hisea/flake/docs/img/plate.jpg

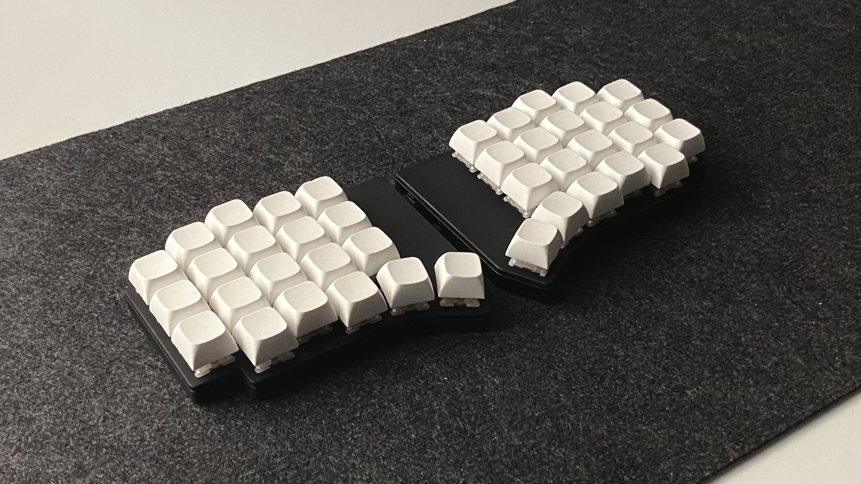
docs/img/plate.jpg
