hisea/flake/docs/img/stacked.jpg

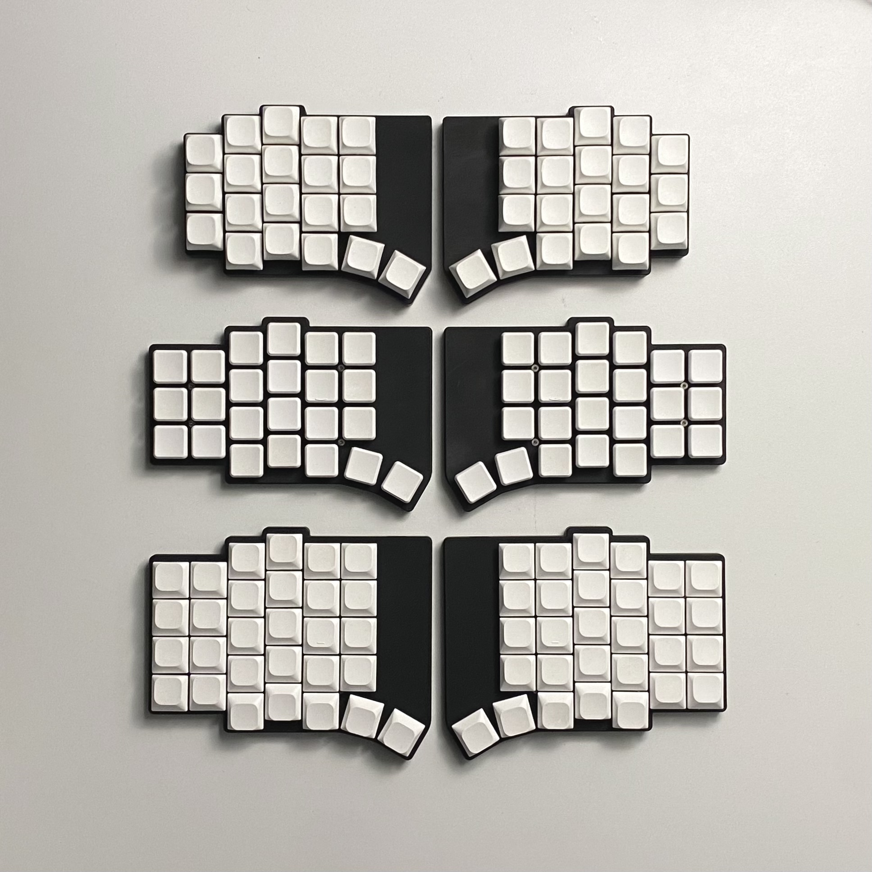
docs/img/stacked.jpg
