hisea/flake/enclosure/L/Enclosure-L.FCStd

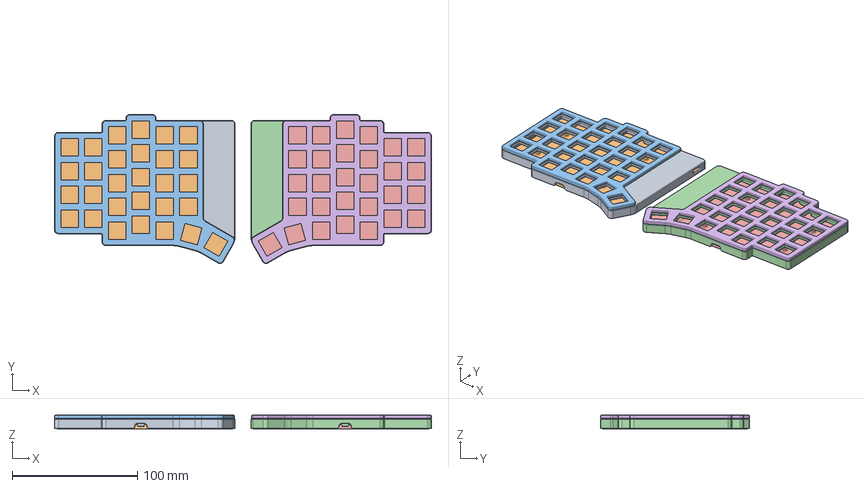
[picture p29: CAD file, 2025-02-06]
enclosure/L/Enclosure-L.FCStd
301.0 x 119.0 x 10.8 mm
Top-Left
Bottom-Left
Plate-Left
Top-Right
Bottom-Right
Plate-Right
