hisea/flake/enclosure/M/Enclosure-M.FCStd

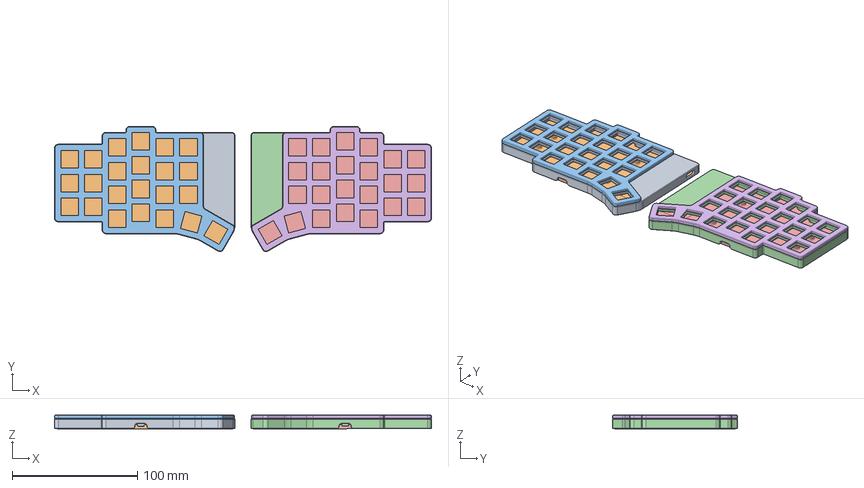
[picture p30: CAD file, 2025-02-06]
enclosure/M/Enclosure-M.FCStd
301.0 x 100.0 x 10.8 mm
Top-Left
Bottom-Left
Plate-Left
Top-Right
Bottom-Right
Plate-Right
