hisea/flake/pcb/L/right.kicad_sch

## KiCad design pcb/L/right.kicad_sch (2025-01-11)

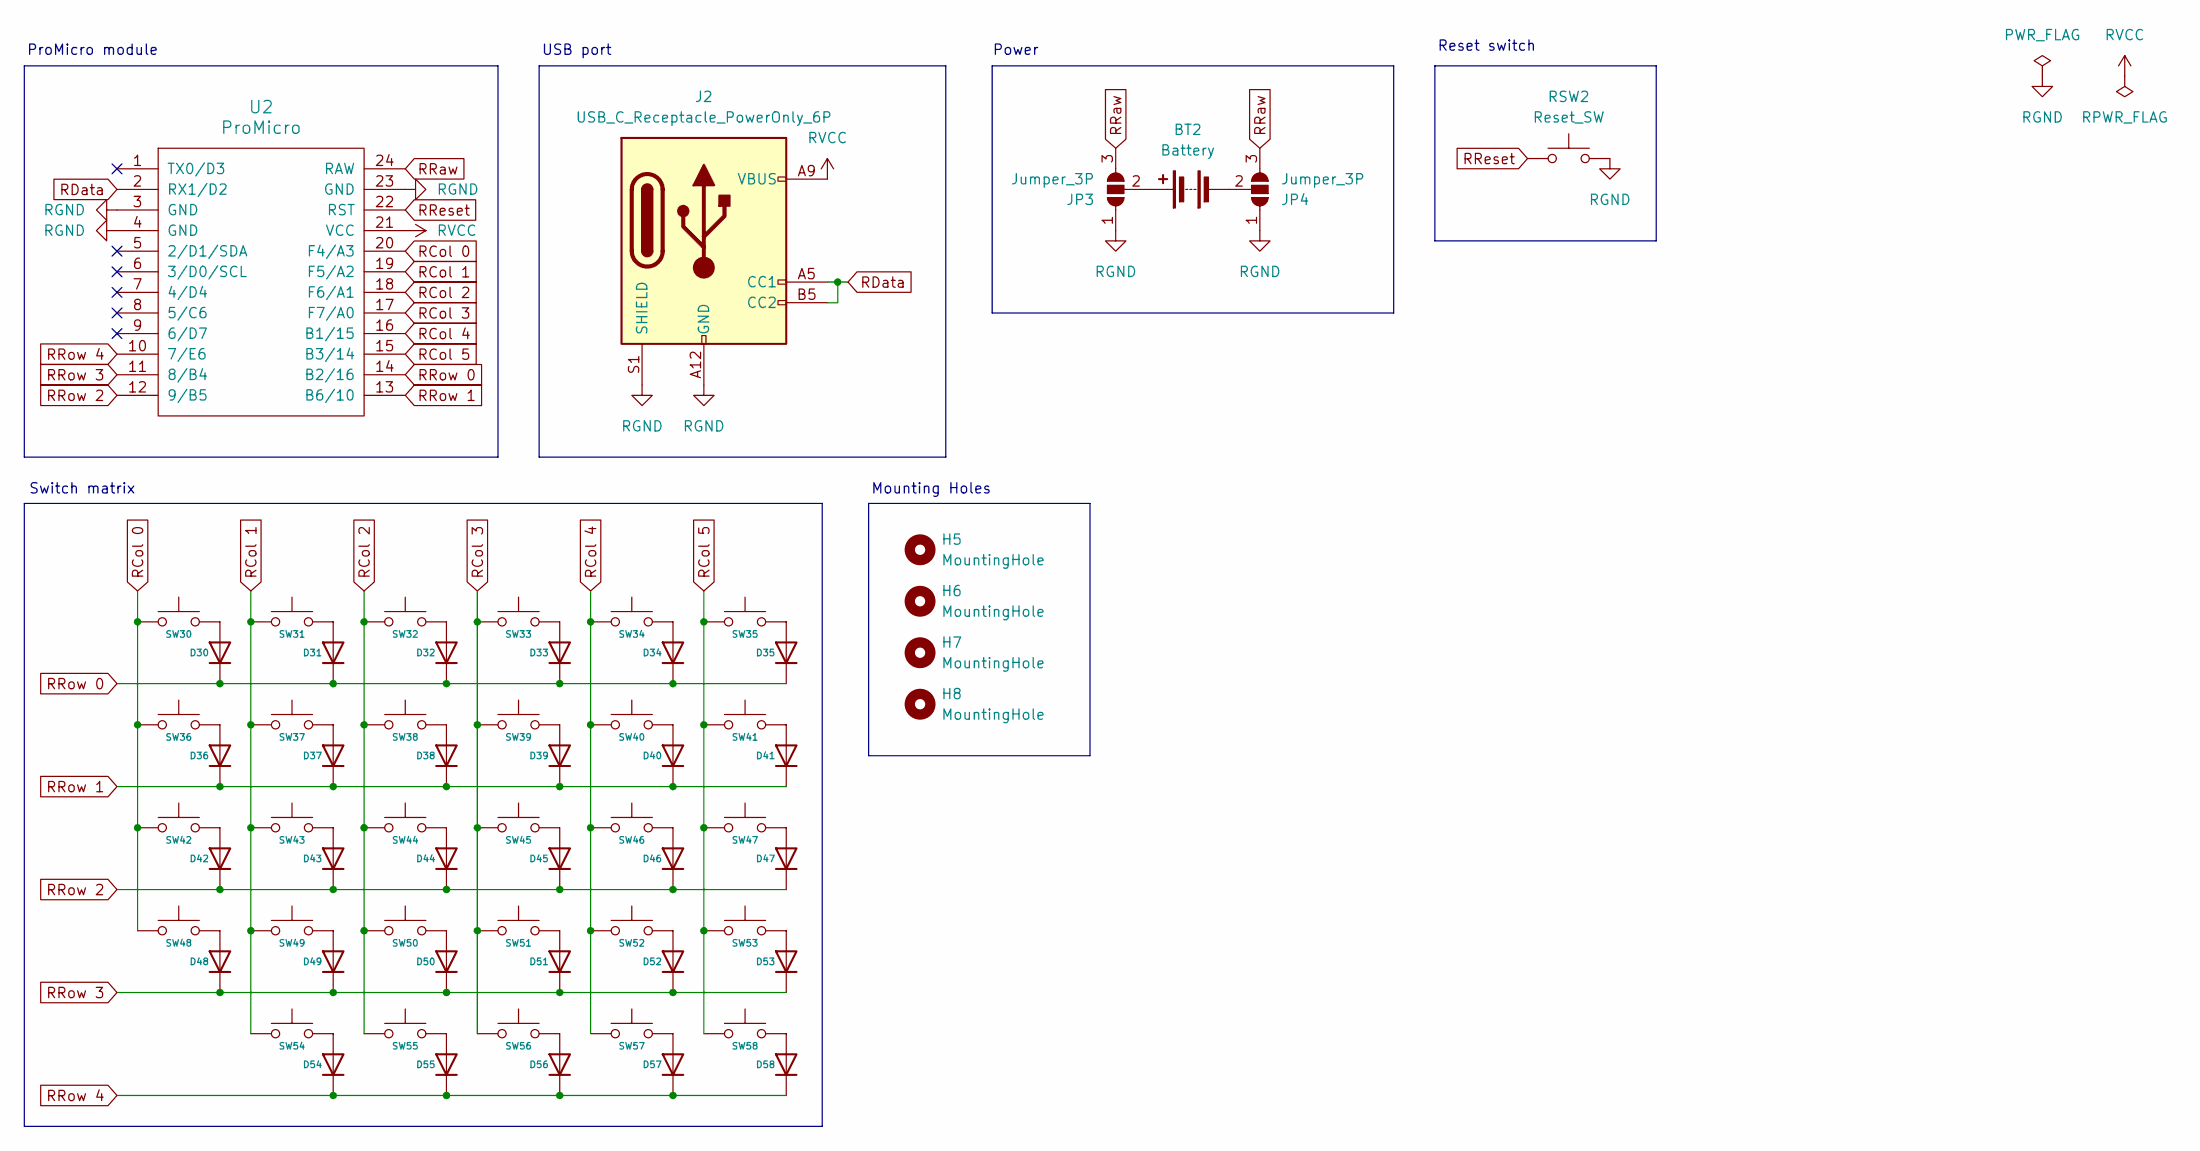
[picture p52: schematic right.kicad_sch]

Parts:
BT2: Battery; JST_1.25mm_mid-mount
D30, D31, D32, D33, D34, D35, D36, D37, D38, D39, D40, D41, D42, D43, D44, D45, D46, D47, D48, D49, D50, D51, D52, D53, D54, D55, D56, D57, D58: D; D_SOD-323_HandSoldering
H5, H6, H7, H8: MountingHole; MountingHole_2.2mm_M2_DIN965
J2: USB_C_Receptacle_PowerOnly_6P; USB-C_6Pin_Mid-mount
JP3, JP4: Jumper_3P; SolderJumper-3_P
RSW2: Reset_SW; TS-1289VE-4
SW30, SW31, SW32, SW33, SW34, SW35, SW36, SW37, SW38, SW39, SW40, SW41, SW42, SW43, SW44, SW45, SW46, SW47, SW48, SW49, SW50, SW51, SW52, SW53, SW54, SW55, SW56, SW57, SW58: SW_Push; SW_MX_Choc-v1v2_Hotswap
U2: ProMicro; ProMicro_SMD

Connections:
unnamed: BT2.1 (+), JP3.2 (C)
unnamed: BT2.2 (-), JP4.2 (C)
unnamed: D30.2 (A), SW30.2
unnamed: D31.2 (A), SW31.2
unnamed: D32.2 (A), SW32.2
unnamed: D33.2 (A), SW33.2
unnamed: D34.2 (A), SW34.2
unnamed: D35.2 (A), SW35.2
unnamed: D36.2 (A), SW36.2
unnamed: D37.2 (A), SW37.2
unnamed: D38.2 (A), SW38.2
unnamed: D39.2 (A), SW39.2
unnamed: D40.2 (A), SW40.2
unnamed: D41.2 (A), SW41.2
unnamed: D42.2 (A), SW42.2
unnamed: D43.2 (A), SW43.2
unnamed: D44.2 (A), SW44.2
unnamed: D45.2 (A), SW45.2
unnamed: D46.2 (A), SW46.2
unnamed: D47.2 (A), SW47.2
unnamed: D48.2 (A), SW48.2
unnamed: D49.2 (A), SW49.2
unnamed: D50.2 (A), SW50.2
unnamed: D51.2 (A), SW51.2
unnamed: D52.2 (A), SW52.2
unnamed: D53.2 (A), SW53.2
unnamed: D54.2 (A), SW54.2
unnamed: D55.2 (A), SW55.2
unnamed: D56.2 (A), SW56.2
unnamed: D57.2 (A), SW57.2
unnamed: D58.2 (A), SW58.2
RCol 0: SW30.1, SW36.1, SW42.1, SW48.1, U2.20 (F4/A3)
RCol 1: SW31.1, SW37.1, SW43.1, SW49.1, SW54.1, U2.19 (F5/A2)
RCol 2: SW32.1, SW38.1, SW44.1, SW50.1, SW55.1, U2.18 (F6/A1)
RCol 3: SW33.1, SW39.1, SW45.1, SW51.1, SW56.1, U2.17 (F7/A0)
RCol 4: SW34.1, SW40.1, SW46.1, SW52.1, SW57.1, U2.16 (B1/15)
RCol 5: SW35.1, SW41.1, SW47.1, SW53.1, SW58.1, U2.15 (B3/14)
RData: J2.A5 (CC1), J2.B5 (CC2), U2.2 (RX1/D2)
RGND: J2.A12 (GND), J2.B12 (GND), J2.S1 (SHIELD), JP3.1 (A), JP4.1 (A), RSW2.2, U2.3 (GND), U2.4 (GND), U2.23 (GND)
RRaw: JP3.3 (B), JP4.3 (B), U2.24 (RAW)
RReset: RSW2.1, U2.22 (RST)
RRow 0: D30.1 (K), D31.1 (K), D32.1 (K), D33.1 (K), D34.1 (K), D35.1 (K), U2.14 (B2/16)
RRow 1: D36.1 (K), D37.1 (K), D38.1 (K), D39.1 (K), D40.1 (K), D41.1 (K), U2.13 (B6/10)
RRow 2: D42.1 (K), D43.1 (K), D44.1 (K), D45.1 (K), D46.1 (K), D47.1 (K), U2.12 (9/B5)
RRow 3: D48.1 (K), D49.1 (K), D50.1 (K), D51.1 (K), D52.1 (K), D53.1 (K), U2.11 (8/B4)
RRow 4: D54.1 (K), D55.1 (K), D56.1 (K), D57.1 (K), D58.1 (K), U2.10 (7/E6)
RVCC: J2.A9 (VBUS), J2.B9 (VBUS), U2.21 (VCC)

Notes on the sheet:
Switch matrix
Mounting Holes
USB port
Power
ProMicro module
Reset switch
