hisea/flake/pcb/M,S/left.kicad_sch

## KiCad design pcb/M,S/left.kicad_sch (2025-06-08)

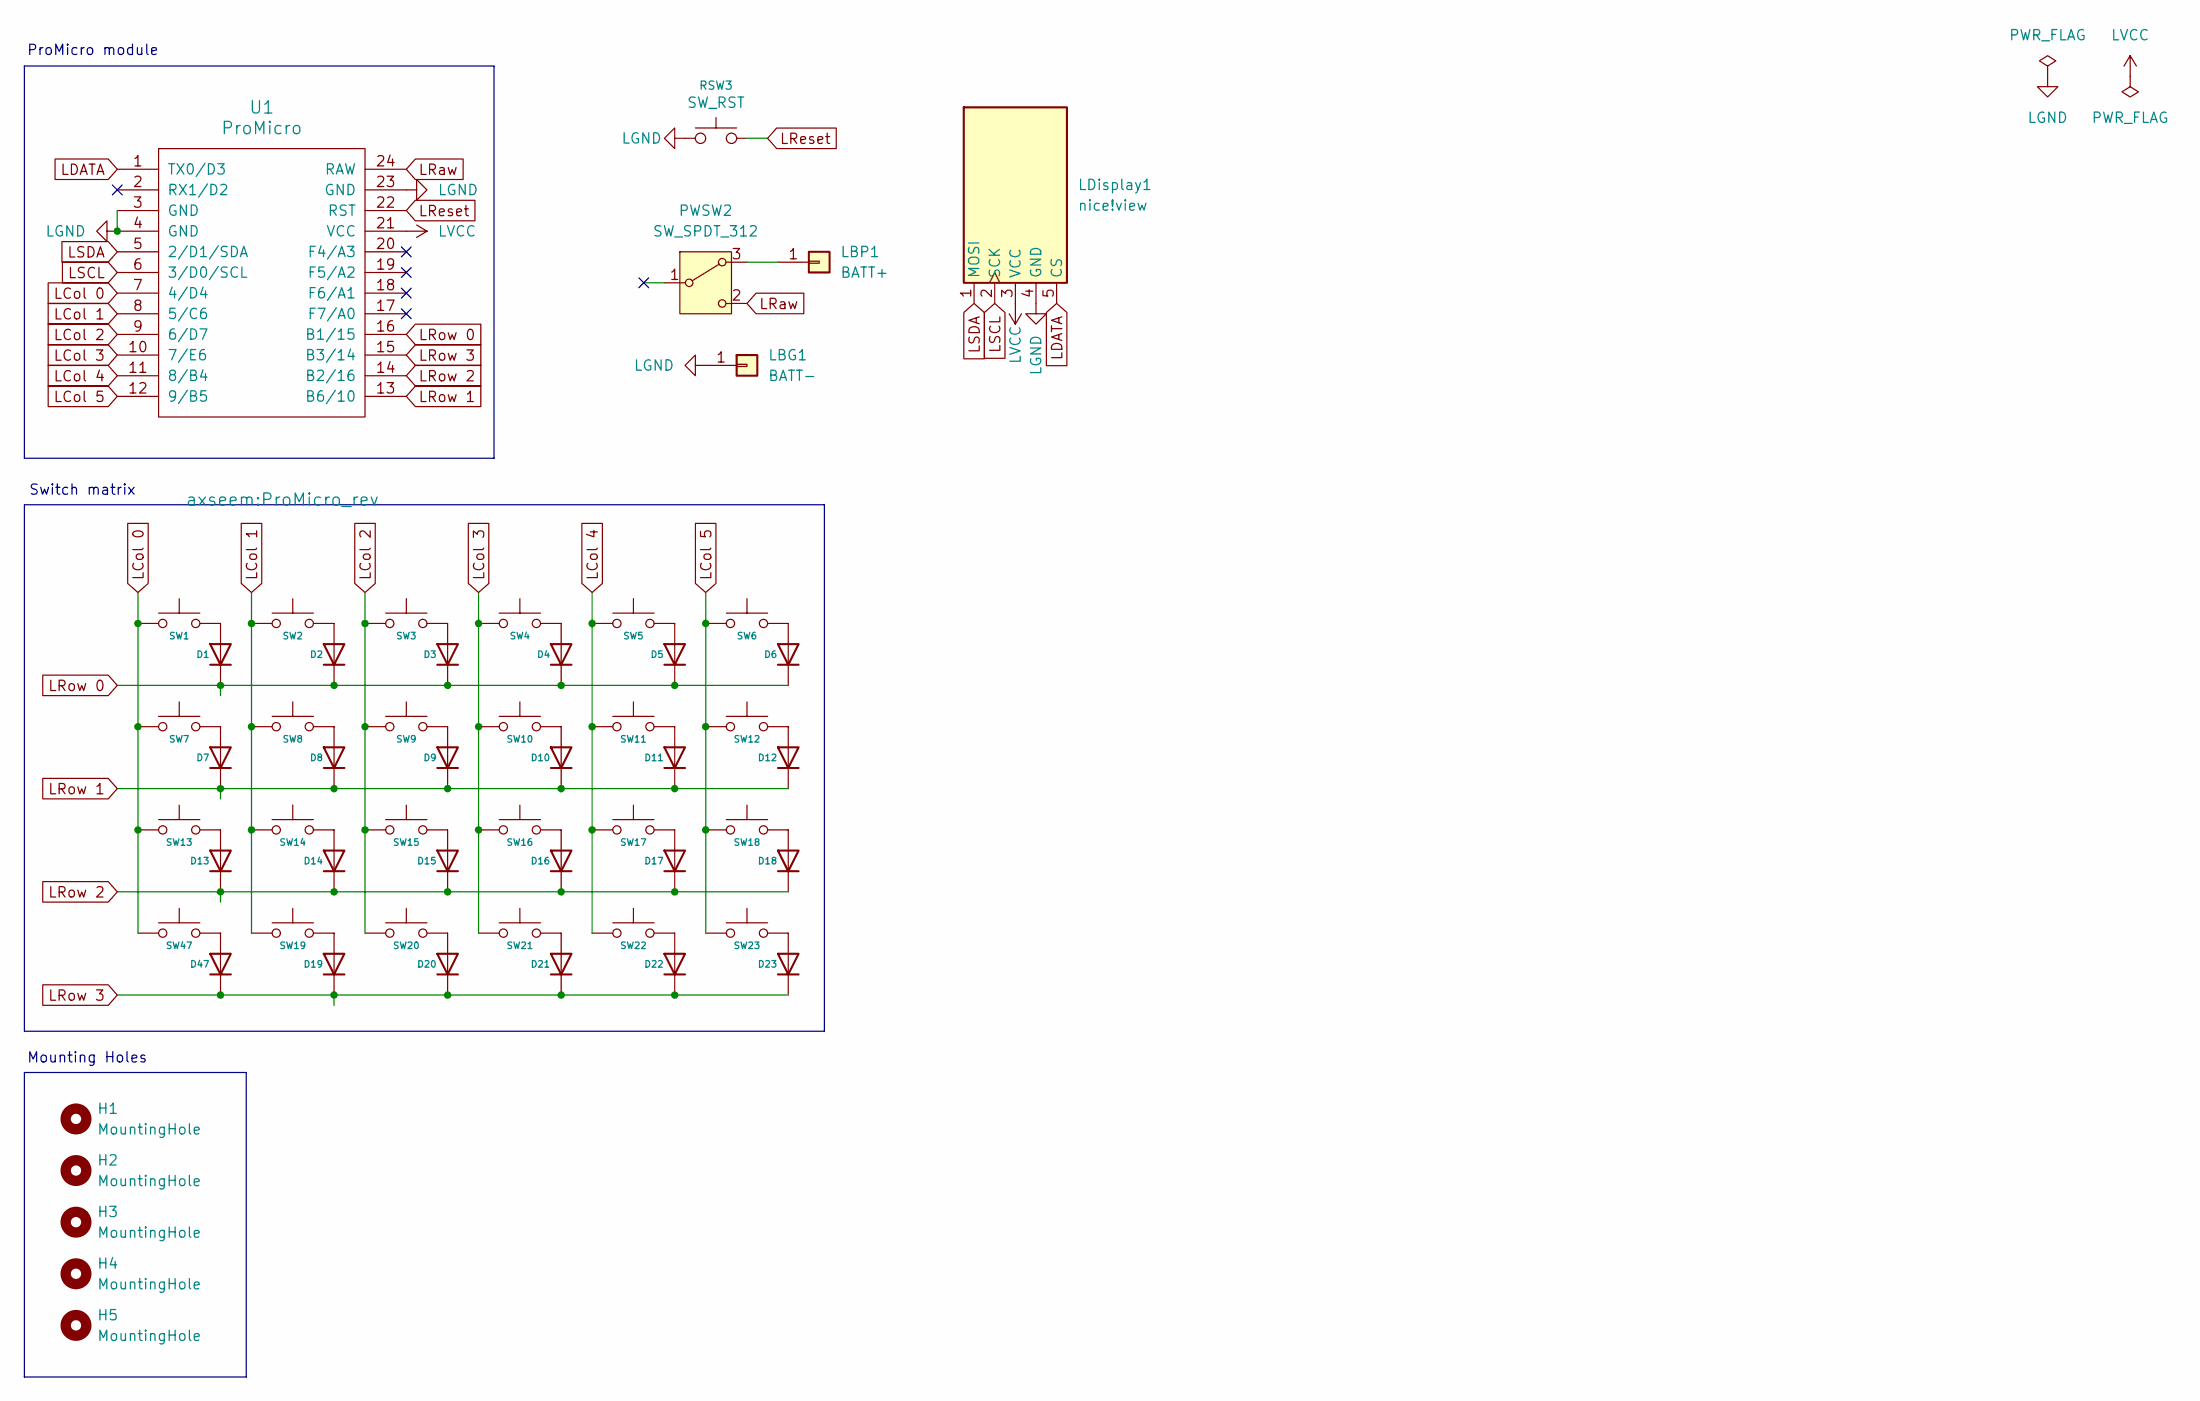
[picture p53: schematic left.kicad_sch]

Parts:
D1, D2, D3, D4, D5, D6, D7, D8, D9, D10, D11, D12, D13, D14, D15, D16, D17, D18, D19, D20, D21, D22, D23, D47: D; D_SOD-323_HandSoldering
H1, H2, H3, H4, H5: MountingHole; MountingHole_2.2mm_M2_DIN965
LBG1: BATT-; 1pin_conn
LBP1: BATT+; 1pin_conn
LDisplay1: nice!view; nice_view_1side
PWSW2: SW_SPDT_312; switch-MSK-12C02-smd
RSW3: SW_RST; TACT_SWITCH_TVBP06
SW1, SW2, SW3, SW4, SW5, SW6, SW7, SW8, SW9, SW10, SW11, SW12, SW13, SW14, SW15, SW16, SW17, SW18, SW19, SW20, SW21, SW22, SW23, SW47: SW_Push; SW_MX_Choc-v1v2_Hotswap
U1: ProMicro; ProMicro_rev

Connections:
LCol 0: SW1.1, SW7.1, SW13.1, SW47.1, U1.7 (4/D4)
LCol 1: SW2.1, SW8.1, SW14.1, SW19.1, U1.8 (5/C6)
LCol 2: SW3.1, SW9.1, SW15.1, SW20.1, U1.9 (6/D7)
LCol 3: SW4.1, SW10.1, SW16.1, SW21.1, U1.10 (7/E6)
LCol 4: SW5.1, SW11.1, SW17.1, SW22.1, U1.11 (8/B4)
LCol 5: SW6.1, SW12.1, SW18.1, SW23.1, U1.12 (9/B5)
LDATA: LDisplay1.5 (CS), U1.1 (TX0/D3)
LGND: LBG1.1, LDisplay1.4 (GND), RSW3.1, U1.3 (GND), U1.4 (GND), U1.23 (GND)
LRaw: PWSW2.2 (C), U1.24 (RAW)
LReset: RSW3.2, U1.22 (RST)
LRow 0: D1.1 (K), D2.1 (K), D3.1 (K), D4.1 (K), D5.1 (K), D6.1 (K), U1.16 (B1/15)
LRow 1: D7.1 (K), D8.1 (K), D9.1 (K), D10.1 (K), D11.1 (K), D12.1 (K), U1.13 (B6/10)
LRow 2: D13.1 (K), D14.1 (K), D15.1 (K), D16.1 (K), D17.1 (K), D18.1 (K), U1.14 (B2/16)
LRow 3: D19.1 (K), D20.1 (K), D21.1 (K), D22.1 (K), D23.1 (K), D47.1 (K), U1.15 (B3/14)
LSCL: LDisplay1.2 (SCK), U1.6 (3/D0/SCL)
LSDA: LDisplay1.1 (MOSI), U1.5 (2/D1/SDA)
LVCC: LDisplay1.3 (VCC), U1.21 (VCC)
unnamed: D1.2 (A), SW1.2
unnamed: D2.2 (A), SW2.2
unnamed: D3.2 (A), SW3.2
unnamed: D4.2 (A), SW4.2
unnamed: D5.2 (A), SW5.2
unnamed: D6.2 (A), SW6.2
unnamed: D7.2 (A), SW7.2
unnamed: D8.2 (A), SW8.2
unnamed: D9.2 (A), SW9.2
unnamed: D10.2 (A), SW10.2
unnamed: D11.2 (A), SW11.2
unnamed: D12.2 (A), SW12.2
unnamed: D13.2 (A), SW13.2
unnamed: D14.2 (A), SW14.2
unnamed: D15.2 (A), SW15.2
unnamed: D16.2 (A), SW16.2
unnamed: D17.2 (A), SW17.2
unnamed: D18.2 (A), SW18.2
unnamed: D19.2 (A), SW19.2
unnamed: D20.2 (A), SW20.2
unnamed: D21.2 (A), SW21.2
unnamed: D22.2 (A), SW22.2
unnamed: D23.2 (A), SW23.2
unnamed: D47.2 (A), SW47.2
unnamed: LBP1.1, PWSW2.3 (A)

Notes on the sheet:
Switch matrix
Mounting Holes
ProMicro module
