hisea/flake/pcb/M,S/right.kicad_sch

## KiCad design pcb/M,S/right.kicad_sch (2025-06-08)

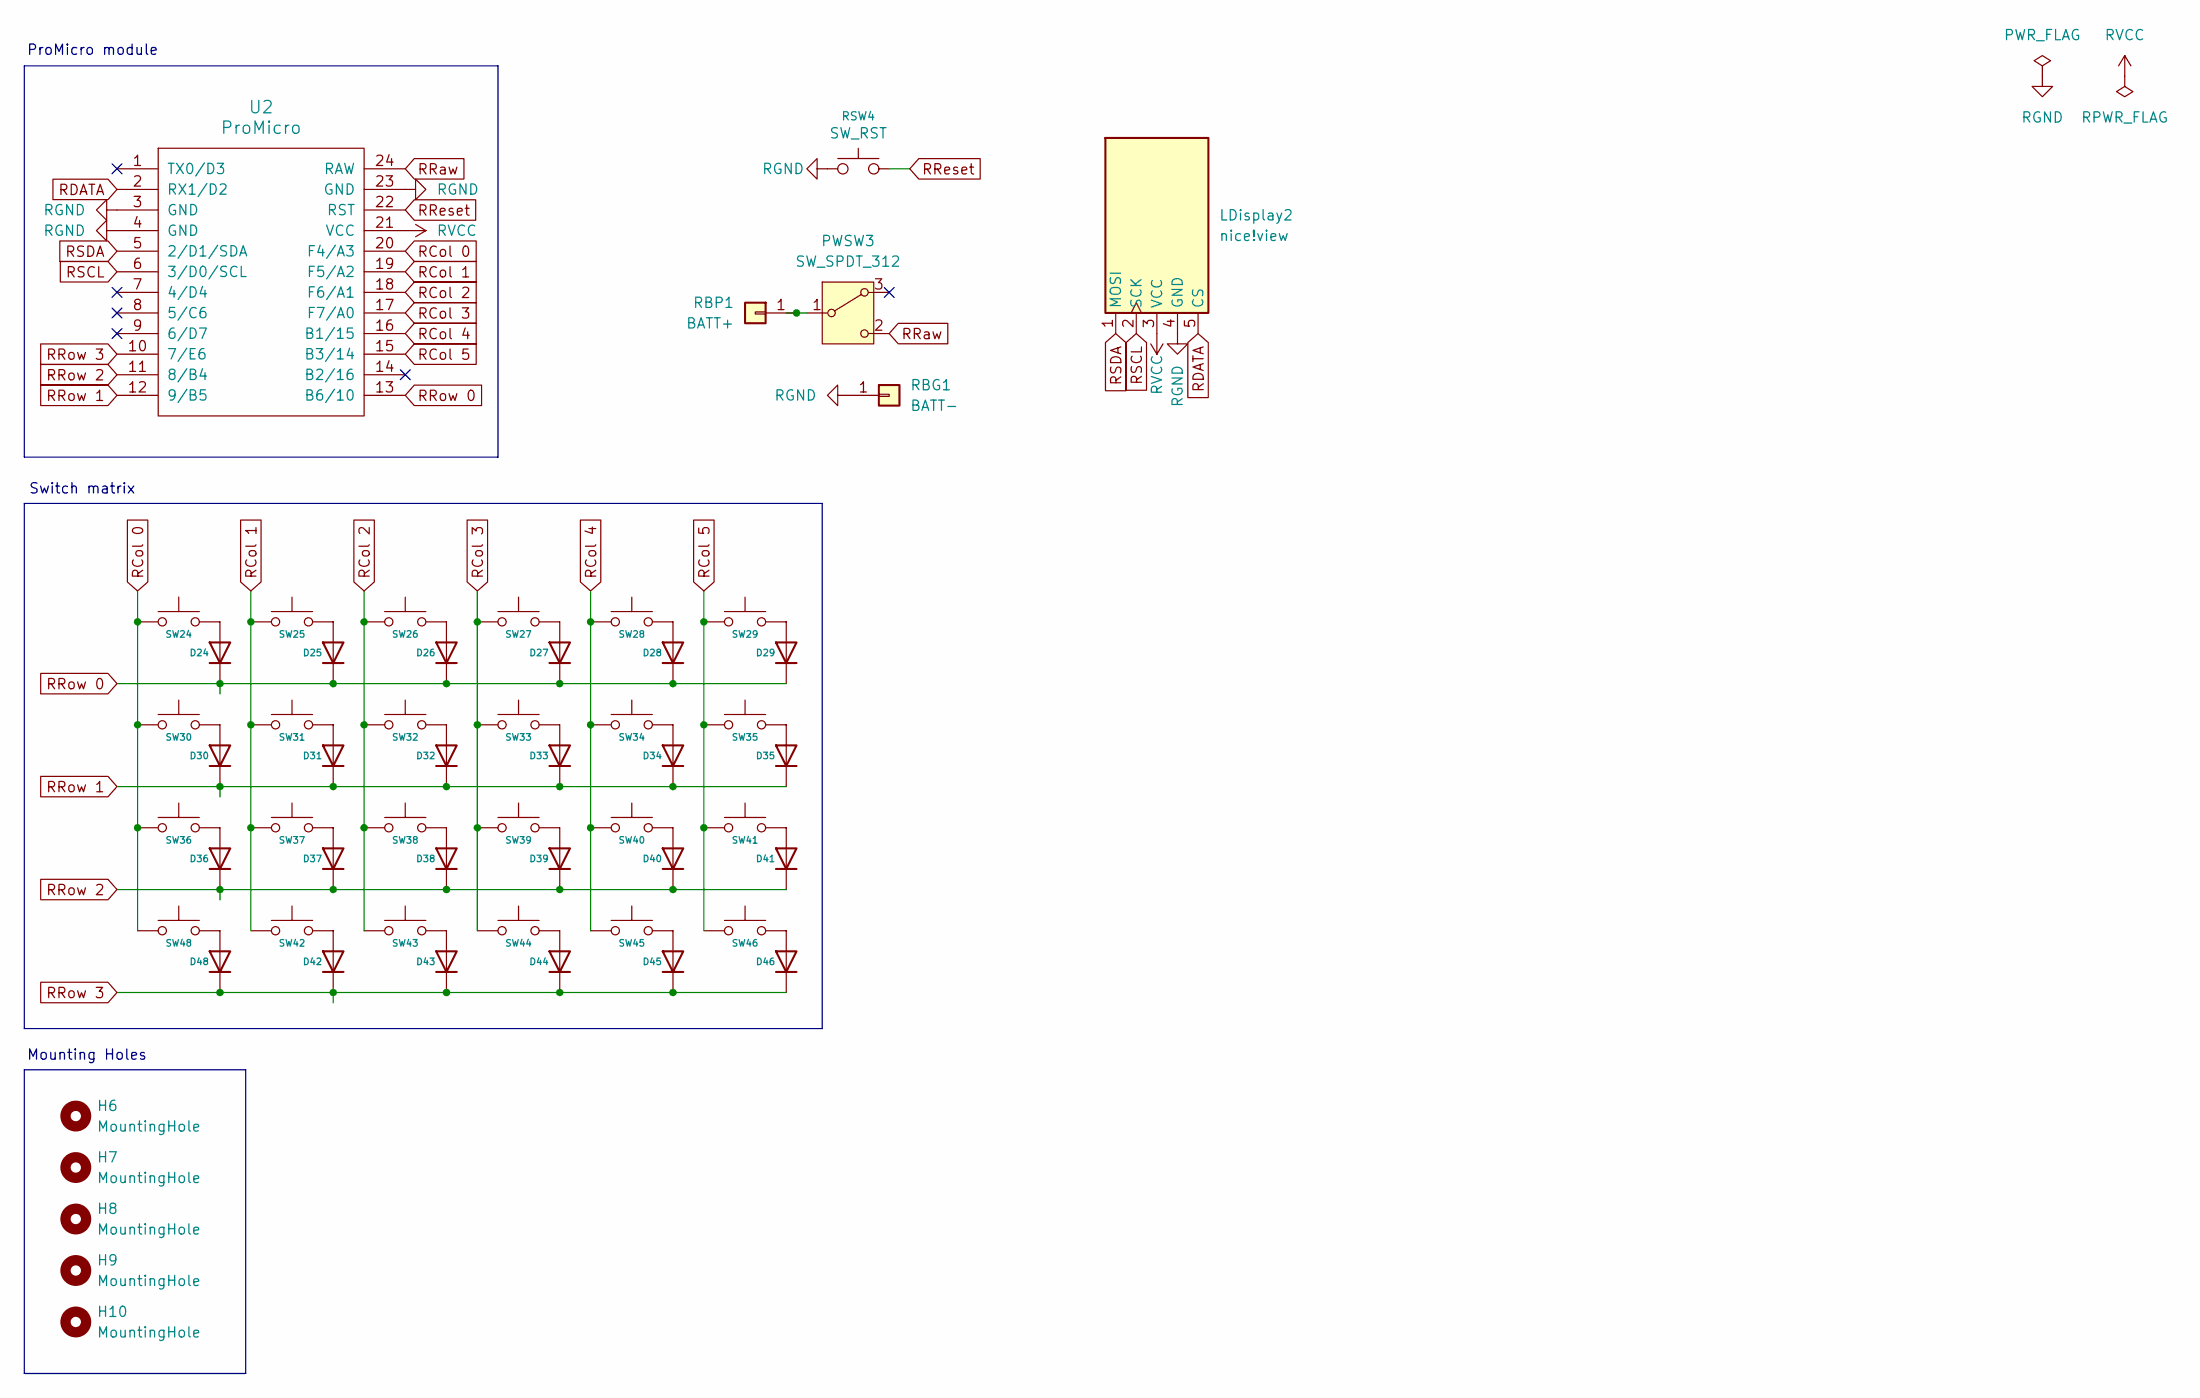
[picture p54: schematic right.kicad_sch]

Parts:
D24, D25, D26, D27, D28, D29, D30, D31, D32, D33, D34, D35, D36, D37, D38, D39, D40, D41, D42, D43, D44, D45, D46, D48: D; D_SOD-323_HandSoldering
H6, H7, H8, H9, H10: MountingHole; MountingHole_2.2mm_M2_DIN965
LDisplay2: nice!view; nice_view_1side
PWSW3: SW_SPDT_312; switch-MSK-12C02-smd
RBG1: BATT-; 1pin_conn
RBP1: BATT+; 1pin_conn
RSW4: SW_RST; TACT_SWITCH_TVBP06
SW24, SW25, SW26, SW27, SW28, SW29, SW30, SW31, SW32, SW33, SW34, SW35, SW36, SW37, SW38, SW39, SW40, SW41, SW42, SW43, SW44, SW45, SW46, SW48: SW_Push; SW_MX_Choc-v1v2_Hotswap
U2: ProMicro; ProMicro_rev

Connections:
unnamed: D24.2 (A), SW24.2
unnamed: D25.2 (A), SW25.2
unnamed: D26.2 (A), SW26.2
unnamed: D27.2 (A), SW27.2
unnamed: D28.2 (A), SW28.2
unnamed: D29.2 (A), SW29.2
unnamed: D30.2 (A), SW30.2
unnamed: D31.2 (A), SW31.2
unnamed: D32.2 (A), SW32.2
unnamed: D33.2 (A), SW33.2
unnamed: D34.2 (A), SW34.2
unnamed: D35.2 (A), SW35.2
unnamed: D36.2 (A), SW36.2
unnamed: D37.2 (A), SW37.2
unnamed: D38.2 (A), SW38.2
unnamed: D39.2 (A), SW39.2
unnamed: D40.2 (A), SW40.2
unnamed: D41.2 (A), SW41.2
unnamed: D42.2 (A), SW42.2
unnamed: D43.2 (A), SW43.2
unnamed: D44.2 (A), SW44.2
unnamed: D45.2 (A), SW45.2
unnamed: D46.2 (A), SW46.2
unnamed: D48.2 (A), SW48.2
unnamed: PWSW3.1 (B), RBP1.1
RCol 0: SW24.1, SW30.1, SW36.1, SW48.1, U2.20 (F4/A3)
RCol 1: SW25.1, SW31.1, SW37.1, SW42.1, U2.19 (F5/A2)
RCol 2: SW26.1, SW32.1, SW38.1, SW43.1, U2.18 (F6/A1)
RCol 3: SW27.1, SW33.1, SW39.1, SW44.1, U2.17 (F7/A0)
RCol 4: SW28.1, SW34.1, SW40.1, SW45.1, U2.16 (B1/15)
RCol 5: SW29.1, SW35.1, SW41.1, SW46.1, U2.15 (B3/14)
RDATA: LDisplay2.5 (CS), U2.2 (RX1/D2)
RGND: LDisplay2.4 (GND), RBG1.1, RSW4.1, U2.3 (GND), U2.4 (GND), U2.23 (GND)
RRaw: PWSW3.2 (C), U2.24 (RAW)
RReset: RSW4.2, U2.22 (RST)
RRow 0: D24.1 (K), D25.1 (K), D26.1 (K), D27.1 (K), D28.1 (K), D29.1 (K), U2.13 (B6/10)
RRow 1: D30.1 (K), D31.1 (K), D32.1 (K), D33.1 (K), D34.1 (K), D35.1 (K), U2.12 (9/B5)
RRow 2: D36.1 (K), D37.1 (K), D38.1 (K), D39.1 (K), D40.1 (K), D41.1 (K), U2.11 (8/B4)
RRow 3: D42.1 (K), D43.1 (K), D44.1 (K), D45.1 (K), D46.1 (K), D48.1 (K), U2.10 (7/E6)
RSCL: LDisplay2.2 (SCK), U2.6 (3/D0/SCL)
RSDA: LDisplay2.1 (MOSI), U2.5 (2/D1/SDA)
RVCC: LDisplay2.3 (VCC), U2.21 (VCC)

Notes on the sheet:
Switch matrix
Mounting Holes
ProMicro module
